bitbarista/word-clock/renders/coupon.png

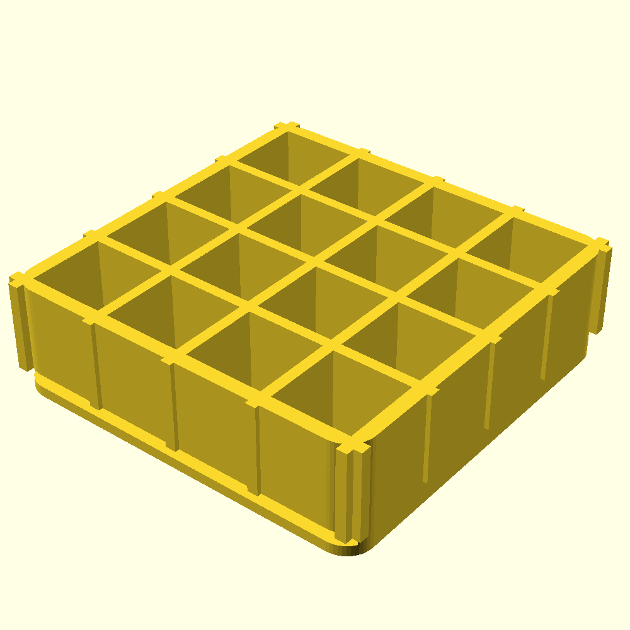
renders/coupon.png
