bitbarista/word-clock/renders/faceplate_front.png

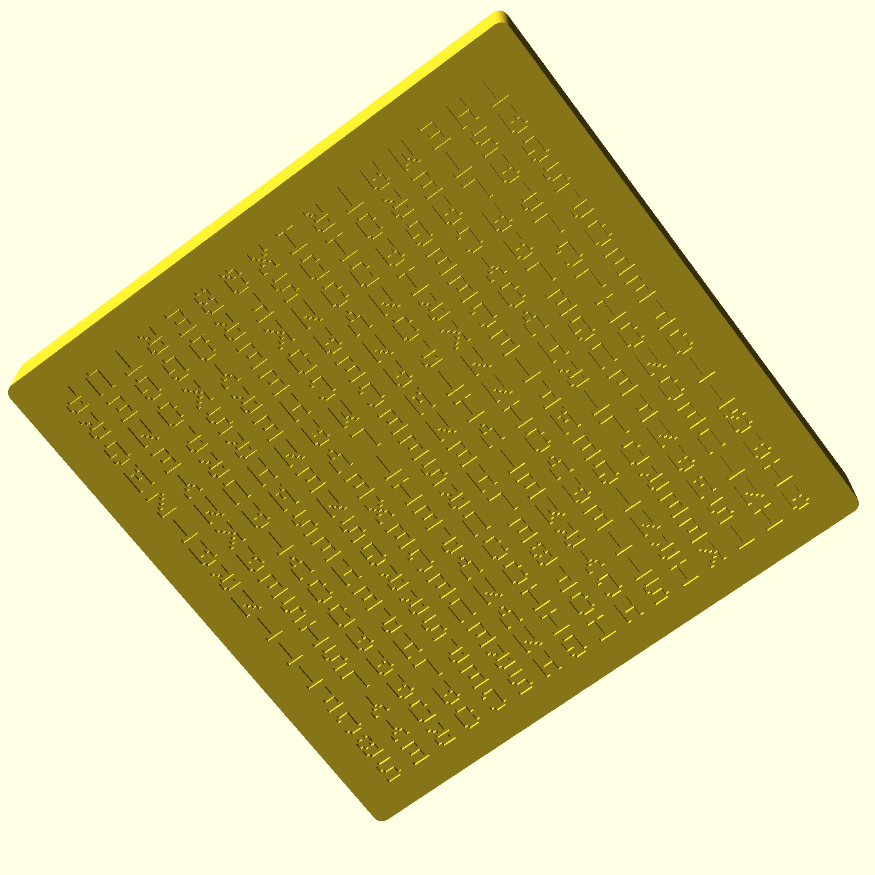
renders/faceplate_front.png
