bitbarista/word-clock/renders/lattice_check.png

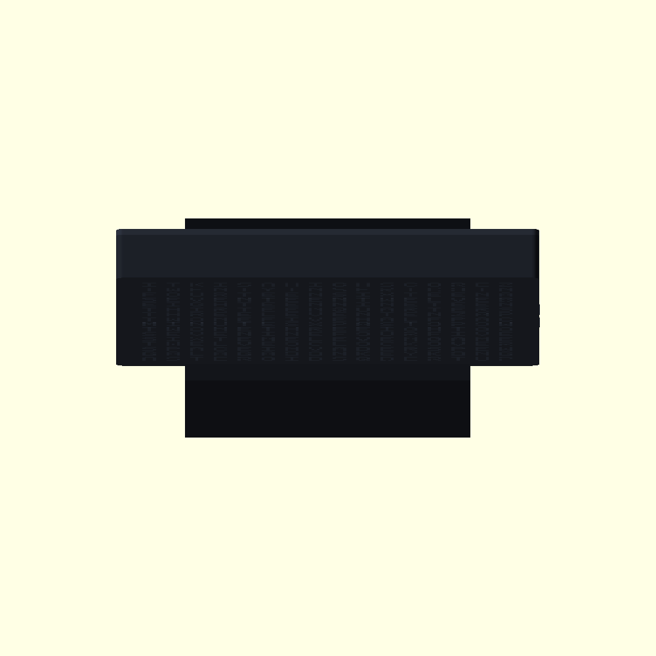
renders/lattice_check.png
