bitbarista/word-clock/renders/pod.png

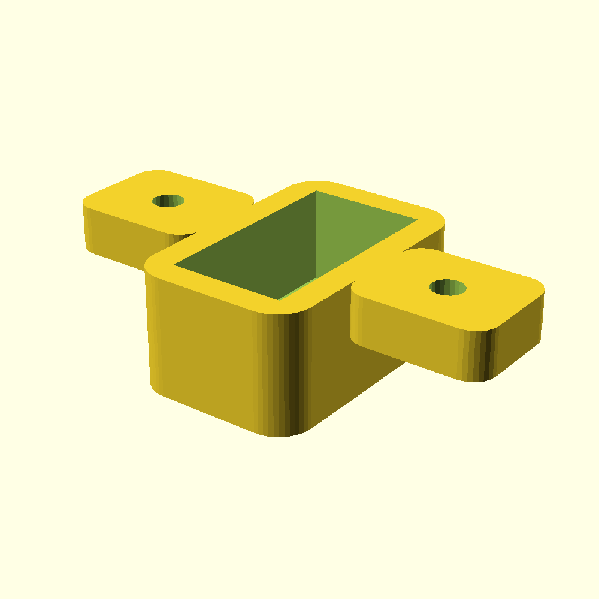
renders/pod.png
