bitbarista/word-clock/renders/shell.png

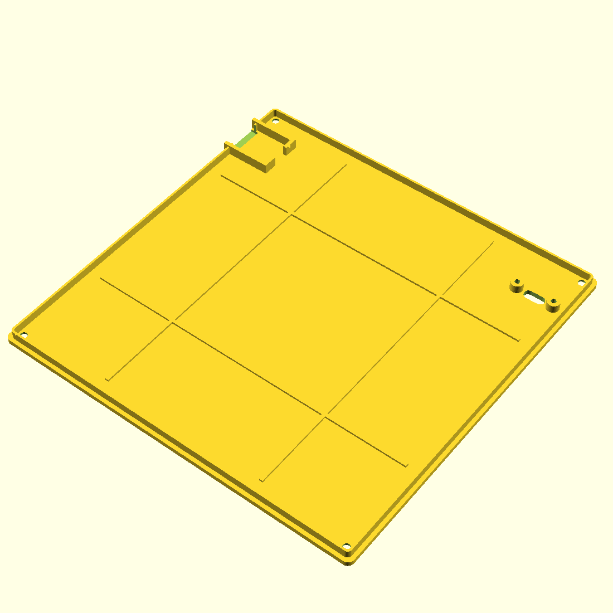
renders/shell.png
