bitbarista/word-clock/renders/stand.png

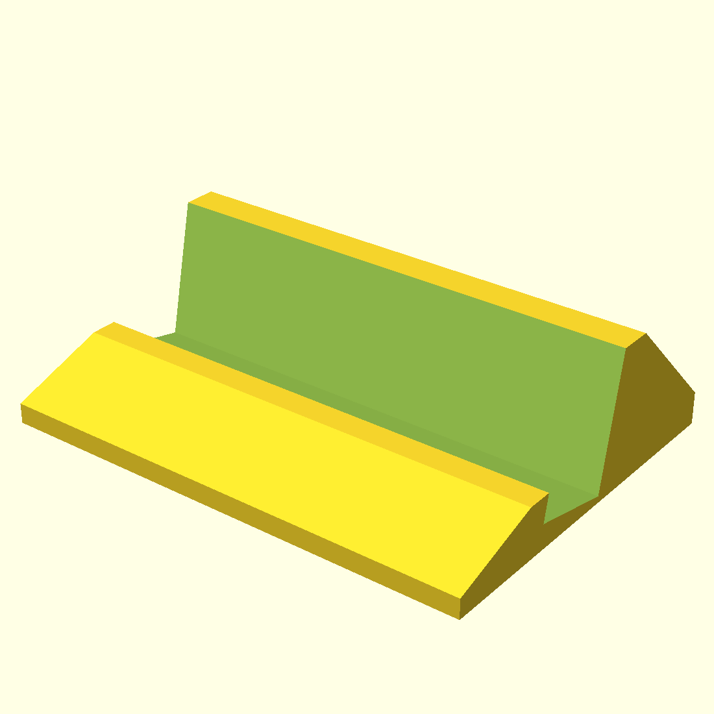
renders/stand.png
