bitbarista/word-clock/renders/usb_corner.png

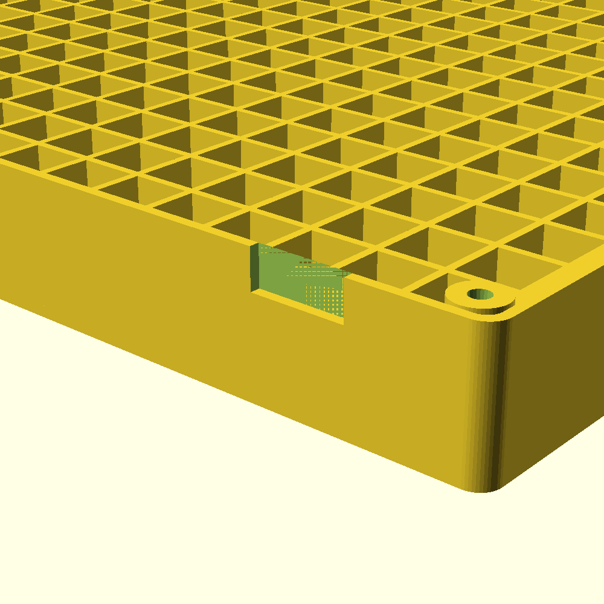
renders/usb_corner.png
