bitbarista/word-clock/renders/assembly_back.png

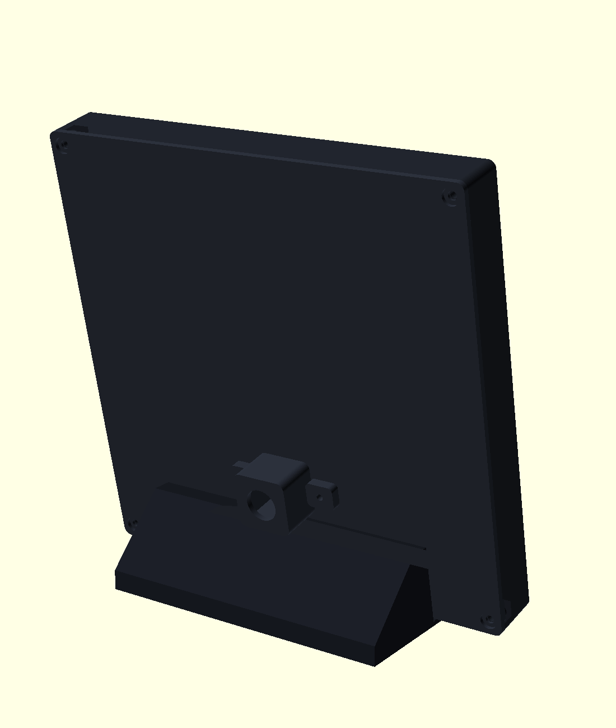
renders/assembly_back.png
