bitbarista/word-clock/renders/assembly_invaders.png

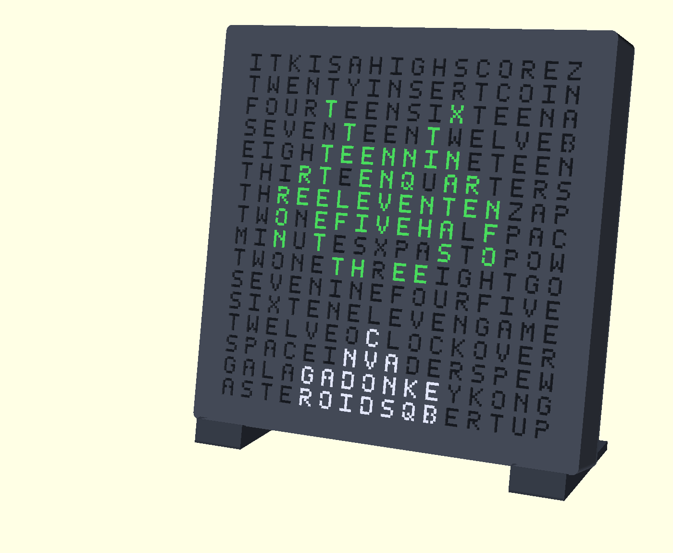
renders/assembly_invaders.png
